sparkfun/MicroMod_Artemis_Processor/TestSketches/I2C1/I2C1.ino

/*
  Reading and controlling the very low power LIS2DH12
  Author: Nathan Seidle
  Created: Septempter 18th, 2019
  License: This code is Lemonadeware; do whatever you want with this code.
  If you see me (or any other SparkFun employee) at the
  local, and you've found our code helpful, please buy us a round!

  This example demonstrates how to read XYZ from the LIS2DH12.

  Feel like supporting open source hardware?
  Buy a board from SparkFun!
  Edge: https://www.sparkfun.com/products/15170
  Edge 2: https://www.sparkfun.com/products/15420
  Qwiic LIS2DH12 Breakout: https://www.sparkfun.com/products/15760

  Hardware Connections:
  Plug a Qwiic cable into the Qwiic Accelerometer RedBoard Qwiic or BlackBoard
  If you don't have a platform with a Qwiic connection use the SparkFun Qwiic Breadboard Jumper (https://www.sparkfun.com/products/14425)
  Open the serial monitor at 115200 baud to see the output
*/

#include <Wire.h>
TwoWire Wire1(1); //Will use pads 8/9

#include "SparkFun_LIS2DH12.h" //Click here to get the library: http://librarymanager/All#SparkFun_LIS2DH12
SPARKFUN_LIS2DH12 accel;       //Create instance

void setup()
{
  Serial.begin(115200);
  Serial.println("SparkFun Accel Example");

  Wire.begin();

  if (accel.begin() == false)
  {
    Serial.println("Accelerometer not detected. Check address jumper and wiring. Freezing...");
    while (1)
      ;
  }
}

void loop()
{
  //Print accel values only if new data is available
  if (accel.available())
  {
    float accelX = accel.getX();
    float accelY = accel.getY();
    float accelZ = accel.getZ();
    float tempC = accel.getTemperature();

    Serial.print("Acc [mg]: ");
    Serial.print(accelX, 1);
    Serial.print(" x, ");
    Serial.print(accelY, 1);
    Serial.print(" y, ");
    Serial.print(accelZ, 1);
    Serial.print(" z, ");
    Serial.print(tempC, 1);
    Serial.print("C");
    Serial.println();

    //    int rawX = accel.getRawX();
    //    int rawY = accel.getRawY();
    //    int rawZ = accel.getRawZ();
    //
    //    Serial.print("Acc raw: ");
    //    Serial.print(rawX);
    //    Serial.print(" x, ");
    //    Serial.print(rawY);
    //    Serial.print(" y, ");
    //    Serial.print(rawZ);
    //    Serial.print(" z");
    //    Serial.println();
  }
}
